tomtebloss/acsi2stm/acsi2stm/TinyFs.cpp

/* ACSI2STM Atari hard drive emulator
 * Copyright (C) 2019-2021 by Jean-Matthieu Coulon
 *
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
 * You should have received a copy of the GNU General Public License
 * along with the program.  If not, see <http://www.gnu.org/licenses/>.
 */

// We are going to torture low-level data structures
// If the library changes too much, it's not guaranteed to work anymore.
#define private public
#include <SdFat.h>
#undef private

#include "Globals.h"

#if ACSI_DRIVER

#include "TinyFs.h"

void TinyPath::getAbsolute(AcsiVolume &volume, AcsiFile *target, oflag_t oflag, AcsiFile *parent) {
  AcsiFile f[2];
  f[0].openRoot(&volume);
  f[1].openRoot(&volume);
  int i = 0;
  for(i = 0; i < maxDepth && f[i & 1] && indexes[i]; ++i) {
    AcsiFile &from = f[i & 1];
    AcsiFile &to = f[~i & 1];
    from.seekSet(((uint32_t)indexes[i] - 1) * 32);
    if(i == maxDepth - 1 || indexes[i + 1] == 0)
      to.openNext(&from, oflag);
    else
      // Directory must be opened in read-only mode
      to.openNext(&from, O_RDONLY);

    if(!to) {
      target->close();
      return;
    }
  }
  *target = f[i & 1];
  if(parent)
    *parent = f[~i & 1];
}

bool TinyPath::getAbsolute(AcsiVolume &volume, char *target, int bufSize) {
  AcsiFile f[2];
  f[0].openRoot(&volume);
  if(!f[0]) {
    // Can't even open root: return empty string
    *target = 0;
    return false;
  }
  *target = '\\';
  ++target;
  --bufSize;
  int i = 0;
  for(i = 0; i < maxDepth && f[i & 1] && indexes[i] && bufSize > 0; ++i) {
    AcsiFile &from = f[i & 1];
    AcsiFile &to = f[~i & 1];
    from.seekSet(((uint32_t)indexes[i] - 1) * 32);
    to.openNext(&from, O_RDONLY);
    if(to) {
      char unicodeName[256];
      to.getName(unicodeName, 256);
      parseUnicodeName(unicodeName);
      int written = nameToAtari(target, bufSize);
      bufSize -= written;
      target += bufSize;
      if(to.isDir() && bufSize) {
        *target = '\\';
        ++target;
        --bufSize;
      }
    }
  }

  // Terminate the string
  if(bufSize > 0)
    *target = 0;
  else
    target[-1] = 0;

  return bufSize > 0;
}

bool TinyPath::set(AcsiVolume &volume, const char *path, int create) {
  // Remove drive letter if any
  if(path[0] && path[1] == ':')
    path += 2;

  int i; // Index in the indexes table;

  if(path[0] == '\\') {
    // Absolute path: start at the beginning
    indexes[0] = 0;
    i = 0;
    ++path;
  } else {
    // Point at the end of the current directory
    for(i = 0; i < maxDepth && indexes[i]; ++i);
  }

  // 2 files to alternate between the two
  AcsiFile f[2];

  // Start with the current path
  getAbsolute(volume, &f[i & 1], O_RDONLY);

  if(!f[i & 1]) {
    indexes[0] = 0;
    return false;
  }

  // Parse path and append to the index list
  while(i < maxDepth - 1 && path[0] && f[i & 1]) {
    AcsiFile &parent = f[i & 1];
    AcsiFile &child = f[~i & 1];

    path = parseAtariPattern(path);
if(create == -1) acsiDbgl("a path=",path," pattern=",pattern," name=",name);

    if(pattern[0] == '.') {
      if(pattern[1] == '.') {
        // "..": Parent directory
        if(i > 0) {
          --i;
          indexes[i] = 0;
          // Need to compute the whole path again to get the parent
          getAbsolute(volume, &child, O_RDONLY);
          if(!child) {
            indexes[0] = 0;
            return false;
          }
        }
      }
      continue;
    }

    // Try to find a matching file

    parent.rewind();
    child.openNext(&parent, O_RDONLY);
    while(child) {
      char childName[256];
      child.getName(childName, 256);
      parseUnicodeName(childName);
      if(matches(pattern))
        break;
      child.openNext(&parent, O_RDONLY);
    }

    if(!child) {
      // No matching file
      if(create) {
        // Check that the name is not a pattern
        for(int i = 0; i < 11; ++i)
          if(pattern[i] == '?')
            // Error: trying to create a file with a wildcard in its name !
            return false;

        // Convert file name to unicode
        char unicodeName[52];
        patternToUnicode(unicodeName, 52);

        if(create == 1) {
          // Create a file
          if(*path)
            // Separator after the file name: a parent directory does not exist.
            return false;

          if(!child.open(&parent, unicodeName, O_RDWR | O_CREAT))
            return false;
        } else if(create == 2) {
          // Create a directory
          if(!child.mkdir(&parent, unicodeName))
            return false;
          if(!child.open(&parent, unicodeName))
            return false;
        } else if(create == -1) {
          // Return true if only the last part is missing
          return !*path;
        }
      }
    }

    if(!child) {
      // Something went wrong, return an error.
      indexes[0] = 0;
      return false;
    }

    indexes[i] = child.dirIndex() + 1;
    ++i;
  }
  indexes[i] = 0;

  return create >= 0;
}

int TinyPath::getNextUnicode(const char *source, char *target) {
  // Forbidden characters
  if(*source && (*source <= ' ' || strchr("*,.:?\\", *source))) {
    *target = '_';
    return 1;
  }

  // Simple 1 byte case
  if(*source < 128) {
    if(*source >= 'a' && *source <= 'z')
      // Convert to upper case
      *target = *source - 'a' + 'A';
    else
      *target = *source;
    return 1;
  }

  // XXX TODO: parse extended unicode and convert it to Atari
  *target = '_';

  // Compute the character length
  int l;
  for(int l = 1; (source[l] & 0b11000000) == 0b1000000; ++l);
  return l;
}

int TinyPath::appendUnicode(char atariChar, char *target, int bufSize) {
  if(bufSize) {
    if(atariChar < 128) {
      *target = atariChar;
      return 1;
    } else {
      // XXX TODO
      *target = '_';
      return 1;
    }
  }
  return 0;
}

int TinyPath::patternToUnicode(char *target, int bufSize) {
  int chars = 0;

  // Expand name
  for(int i = 0; i < 8 && chars < bufSize && pattern[i] != ' '; ++i)
    chars += appendUnicode(pattern[i], &target[chars], bufSize - chars);

  if(pattern[8] != ' ' && chars < bufSize) {
    target[chars] = '.';
    ++chars;
  }

  // Expand extension
  for(int i = 8; i < 11 && chars < bufSize && pattern[i] != ' '; ++i)
    chars += appendUnicode(pattern[i], &target[chars], bufSize - chars);

  // Terminate target string
  if(chars < bufSize) {
    target[chars] = '\0';
    ++chars;
  }

  acsiDbgl("XXX patternToUnicode pattern=",pattern," target=",target);

  return chars;
}

int TinyPath::nameToAtari(char *target, int bufSize) {
  int chars = 0;

  // Expand name
  for(int i = 0; i < 8 && chars < bufSize && name[i] != ' '; ++i) {
    target[chars] = name[i];
    ++chars;
  }

  // Append extension dot if needed
  if(name[8] != ' ' && chars < bufSize) {
    target[chars] = '.';
    ++chars;
  }

  // Expand extension
  for(int i = 8; i < 11 && chars < bufSize && name[i] != ' '; ++i) {
    target[chars] = name[i];
    ++chars;
  }

  return chars;
}

int TinyPath::nameToAtari(AcsiFile *file, char *target, int bufSize) {
  char unicodeName[256];
  file->getName(unicodeName, 256);
  parseUnicodeName(unicodeName);
  return nameToAtari(target, bufSize);
}

bool TinyPath::matches(const char pattern[11]) {
  for(int i = 0; i < 11; ++i) {
    if(pattern[i] != '?' && pattern[i] != name[i])
      return false;
  }
  
  return true;
}

const char * TinyPath::parseAtariPattern(const char *path) {
  int i = 0; // Index in the source string
  int j = 0; // Index in name

  // Parse name
  for(i = 0, j = 0; j < 8 && path[i] && path[i] != '\\' && path[i] != '.'; ++i, ++j) {
    if(path[i] == '*') {
      // Fill with '?' until the end
      for(; j < 8; ++j)
        pattern[j] = '?';
      ++i;
      break;
    }
    pattern[j] = path[i];
  }

  // Fill the name with spaces
  for(; j < 8; ++j)
    pattern[j] = ' ';

  // Point at the first letter of the extension
  while(path[i] && path[i] != '\\' && path[i] != '.')
    ++i;
  if(path[i] == '.')
    ++i;

  // Parse extension
  for(; j < 11 && path[i] && path[i] != '\\'; ++i, ++j) {
    if(path[i] == '*') {
      // Fill with '?' until the end
      for(; j < 11; ++j)
        pattern[j] = '?';
      ++i;
      break;
    }
    pattern[j] = path[i];
  }

  // Fill the extension with spaces
  for(; j < 11; ++j)
    pattern[j] = ' ';

  if(path[i] == '\\')
    ++i;

  return &path[i];
}

const char * TinyPath::parseUnicodeName(const char *path) {
  int i = 0; // Index in the source string
  int j = 0; // Index in name

  int nameEnd;
  int ext;

  // Find the end of the current name
  for(nameEnd = 0; path[nameEnd] && path[nameEnd] != '/'; ++nameEnd);

  // Find the extension
  for(ext = nameEnd - 1; ext > 0 && path[ext] != '.'; --ext);

  if(path[ext] != '.')
    // No extension, put the extension pointer just before the end
    ext = nameEnd;

  // Parse name
  for(i = 0, j = 0; i < ext && j < 8; ++j) {
    if(path[i] == '*') {
      // Fill with '?' until the end
      for(; j < 8; ++j)
        name[j] = '?';
      ++i;
      break;
    }
    i += getNextUnicode(&path[i], &name[j]);
  }

  // Fill the name with spaces
  for(; j < 8; ++j)
    name[j] = ' ';

  // Parse extension
  if(path[ext] == '.') {
    for(i = ext + 1; i < nameEnd && j < 11; ++j) {
      if(path[i] == '*') {
        // Fill with '?' until the end
        for(; j < 11; ++j)
          name[j] = '?';
        ++i;
        break;
      }
      i += getNextUnicode(&path[i], &name[j]);
    }
  }

  // Fill the extension with spaces
  for(; j < 11; ++j)
    name[j] = ' ';

  if(path[nameEnd] == '/')
    ++nameEnd;

  return &path[nameEnd];
}

char TinyPath::name[11];
char TinyPath::pattern[11];

AcsiFile * TinyFile::open(AcsiVolume &volume, TinyPath & path, oflag_t oflag) {
  close();

  path.getAbsolute(volume, &g.f, oflag, &g.dir);

  if(g.f) {
    index = g.f.dirIndex() + 1;
    if(g.dir.isSubDir())
      dirCluster = getCluster(g.dir);
    else
      dirCluster = 0;
    g.dir.seekSet(((uint32_t)index - 1) * 32);
  } else {
    index = 0;
  }

  return &g.f;
}

AcsiFile * TinyFile::acquire(AcsiVolume &volume, oflag_t oflag) {
  if(index
     && g.lastAcquiredCluster == dirCluster
     && g.lastAcquiredIndex == index
     && g.f
     && g.dir
     && ((oflag & O_RDWR) ? g.f.isWritable() : true)
  ) {
    // Optimized !
    return &g.f;
  }

  g.f.close();

  if(!index) {
    // File closed
    g.lastAcquiredIndex = 0;
    return &g.f;
  }

  // Open the parent directory in g.dir
  if(!dirCluster) {
    // File is in the root directory
    g.dir.openRoot(&volume);
  } else {
    // Find any directory to inject data into the structure (evil grin)
    g.f.openRoot(&volume);
    while(g.dir.openNext(&g.f, O_RDONLY) && !g.dir.isDirectory());
    if(g.dir) {
      // Found a directory handle to inject the cluster in it
      setCluster(g.dir, dirCluster);
    } else {
      // Should never happen
      close();
    }
  }

  // Find the file with the correct index
  g.f.open(&g.dir, index - 1, oflag);

  if(g.f) {
    g.lastAcquiredCluster = dirCluster;
    g.lastAcquiredIndex = index;
  } else {
    g.lastAcquiredIndex = 0;
  }

  return &g.f;
}

void TinyFile::close() {
  g.f.close();
  index = 0;
  g.lastAcquiredIndex = 0;
}

AcsiFile * TinyFile::openNext(AcsiVolume &volume, oflag_t oflag, const char pattern[11]) {
  acquire(volume, O_RDONLY);

  if(!g.f) {
    close();
    return &g.f;
  }

  if(g.dir)
    findNextMatching(pattern, oflag);

  // Update the index
  if(g.f)
    index = g.f.dirIndex() + 1;
  else
    index = 0;

  return &g.f;
}

AcsiFile * TinyFile::openFirst(AcsiVolume &volume, oflag_t oflag, const char pattern[11]) {
  close();

  if(g.dir) {
    g.dir.rewind();
    findNextMatching(pattern, oflag);
  }

  // Update the index
  if(g.f) {
    index = g.f.dirIndex() + 1;
    g.dir.seekSet(((uint32_t)index - 1) * 32);
  } else {
    index = 0;
  }

  return &g.f;
}

AcsiFile * TinyFile::openFirst(AcsiVolume &volume, TinyPath &path, oflag_t oflag, const char pattern[11]) {
  close();

  path.getAbsolute(volume, &g.dir);
  if(g.dir)
    findNextMatching(pattern, oflag);

  if(g.f) {
    index = g.f.dirIndex() + 1;
    if(g.dir.isSubDir())
      dirCluster = getCluster(g.dir);
    else
      dirCluster = 0;
  } else {
    index = 0;
  }

  return &g.f;
}

void TinyFile::findNextMatching(const char pattern[11], oflag_t oflag) {
  g.f.openNext(&g.dir, oflag);
  while(g.f) {
    char name[256];
    g.f.getName(name, 256);
    TinyPath::parseUnicodeName(name);
    if(TinyPath::matches(pattern))
      break;
    g.f.openNext(&g.dir, oflag);
  }
}

uint32_t TinyFile::getCluster(AcsiFile &f) {
  uint32_t cluster;
  uint64_t position = f.curPosition();
  f.rewind();
  if(f.m_fFile)
    cluster = f.m_fFile->m_firstCluster;
  else
    cluster = f.m_xFile->m_firstCluster;
  f.seekSet(position);
  return cluster;
}

void TinyFile::setCluster(AcsiFile &f, uint32_t cluster) {
  f.rewind();
  if(f.m_fFile)
    f.m_fFile->m_firstCluster = cluster;
  else
    f.m_xFile->m_firstCluster = cluster;
}

// Global variables for TinyFile
TinyFile::Global TinyFile::g;

int TinyFileDescriptor::read(AcsiVolume &volume, uint8_t *data, int bytes) {
  AcsiFile *f = acquire(volume);
  if(!f->seekSet(position))
    return -1;

  int r = f->read(data, bytes);
  if(r > 0)
    position += r;

  return r;
}

int TinyFileDescriptor::write(AcsiVolume &volume, uint8_t *data, int bytes) {
  AcsiFile *f = acquire(volume, O_RDWR);
  if(!f->seekSet(position))
    return -1;

  int r = f->write(data, bytes);
  if(r > 0)
    position += r;

  return r;
}

#endif
