tomtebloss/acsi2stm/acsi2stm/DmaPort.h

/* ACSI2STM Atari hard drive emulator
 * Copyright (C) 2019-2021 by Jean-Matthieu Coulon
 *
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
 * You should have received a copy of the GNU General Public License
 * along with the program.  If not, see <http://www.gnu.org/licenses/>.
 */

#ifndef DMA_PORT_H
#define DMA_PORT_H

#include "Globals.h"
#include "Watchdog.h"

struct DmaPort {
  static void init();
  void begin(uint8_t deviceMask = 0);

  // Add a device ID to the mask
  void addDevice(int id) {
    deviceMask |= 1<<id;
  }

  // Remove a device ID from the mask
  void removeDevice(int id) {
    deviceMask &=~ (1<<id);
  }

  // Return true if the ACSI bus is idle:
  // IRQ, DRQ and ACK are high.
  static bool idle();

  // Wait until the bus is ready.
  // Uses input pull-down to detect that the ST is actually powered on.
  void waitBusReady();

  // Wait for a command on the bus.
  //
  // This function never never fails but may trigger the watchdog.
  // Returns the command byte. You can use cmdDeviceId and cmdCommand to parse it.
  uint8_t waitCommand();

  // Returns the device ID for a given command byte.
  static uint8_t cmdDeviceId(uint8_t cmd) {
    return cmd >> 5;
  }

  // Read bytes using the IRQ/CS method.
  static void readIrq(uint8_t *bytes, int count);

  // Read one byte using the IRQ/CS method.
  static uint8_t readIrq();

  // Send one byte using the IRQ/CS method.
  // This is normally used for the status byte.
  static void sendIrq(uint8_t byte);

  // Read bytes using the DRQ/ACK method.
  // count must be a multiple of 16.
  static void read(uint8_t *bytes, int count);

  // Read to dataBuf.
  void read(int count = ACSI_BLOCKSIZE) {
    read(dataBuf, count);
  }

  // Send bytes using the DRQ/ACK method.
  // count must be a multiple of 16.
  static void send(const uint8_t *bytes, int count);
  
  // Send data in dataBuf.
  void send(int count = ACSI_BLOCKSIZE) {
    send(dataBuf, count);
  }

  Watchdog watchdog;

  uint8_t dataBuf[ACSI_BLOCKSIZE];
protected:
  // Low level pin manipulation methods
  static void releaseDrq();
  static void releaseIrq();
  static void releaseDataBus();
  static void acquireDrq();
  static void acquireDataBus();
  static uint8_t waitCs();
  static uint8_t waitA1();
  static bool readAck();
  static void pullIrq();
  static bool pullDrqUntilAck();
  static void writeData(uint8_t byte);

  // Device initialization
  static void setupDrqTimer();
  static void setupCsTimer();
  static void setupGpio();

public: // XXX
  uint8_t deviceMask;
};

// vim: ts=2 sw=2 sts=2 et
#endif
