tomtebloss/acsi2stm/acsi2stm/boot.h

unsigned char boot_bin[] = {
  0x48, 0xe7, 0xff, 0xfe, 0x41, 0xfa, 0x01, 0x62, 0x8f, 0x10, 0xea, 0x0f,
  0x41, 0xfa, 0x01, 0x6b, 0xdf, 0x10, 0x48, 0x79, 0x00, 0x00, 0x0c, 0x00,
  0x3f, 0x3c, 0x00, 0x48, 0x4e, 0x41, 0x5c, 0x4f, 0x4a, 0x80, 0x67, 0x42,
  0x2c, 0x40, 0x61, 0x00, 0x00, 0xba, 0x4a, 0x00, 0x66, 0x26, 0x2f, 0x3c,
  0x00, 0x00, 0x0b, 0xde, 0x2f, 0x0e, 0x3f, 0x3c, 0x00, 0x4a, 0x4e, 0x41,
  0x4f, 0xef, 0x00, 0x0a, 0x4e, 0x96, 0x4a, 0x00, 0x67, 0x28, 0x2f, 0x0e,
  0x3f, 0x3c, 0x00, 0x49, 0x4e, 0x41, 0x5c, 0x4f, 0x60, 0x00, 0x00, 0x1c,
  0x2f, 0x0e, 0x3f, 0x3c, 0x00, 0x49, 0x4e, 0x41, 0x5c, 0x4f, 0x48, 0x7a,
  0x01, 0x43, 0x60, 0x00, 0x00, 0x64, 0x48, 0x7a, 0x01, 0x2b, 0x60, 0x00,
  0x00, 0x5c, 0x41, 0xfa, 0xff, 0x90, 0x4a, 0x28, 0x01, 0xb5, 0x67, 0x64,
  0x11, 0x7c, 0x00, 0x20, 0x01, 0x69, 0x11, 0x7c, 0x00, 0x01, 0x01, 0x6c,
  0x43, 0xe8, 0x02, 0x00, 0x30, 0x3c, 0x00, 0x7f, 0x22, 0xd8, 0x51, 0xc8,
  0xff, 0xfc, 0x43, 0xfa, 0xff, 0x6c, 0x20, 0x09, 0x60, 0x00, 0x02, 0x02,
  0x61, 0x44, 0x4a, 0x00, 0x67, 0x06, 0x48, 0x7a, 0x00, 0xe2, 0x60, 0x20,
  0x48, 0x7a, 0x00, 0xc3, 0x3f, 0x3c, 0x00, 0x09, 0x4e, 0x41, 0x5c, 0x4f,
  0x48, 0x7a, 0x00, 0xc6, 0x3f, 0x3c, 0x00, 0x09, 0x4e, 0x41, 0x5c, 0x4f,
  0x4c, 0xdf, 0x7f, 0xff, 0x60, 0x00, 0xfd, 0x3a, 0x48, 0x7a, 0x00, 0xa3,
  0x3f, 0x3c, 0x00, 0x09, 0x4e, 0x41, 0x5c, 0x4f, 0x3f, 0x3c, 0x00, 0x09,
  0x4e, 0x41, 0x5c, 0x4f, 0x4c, 0xdf, 0x7f, 0xff, 0x4e, 0x75, 0x50, 0xf8,
  0x04, 0x3e, 0x41, 0xfa, 0x00, 0x80, 0x43, 0xf8, 0x86, 0x06, 0x45, 0xf8,
  0x86, 0x04, 0x32, 0xbc, 0x01, 0x90, 0x32, 0xbc, 0x00, 0x90, 0x11, 0xc0,
  0x86, 0x0d, 0xe0, 0x88, 0x11, 0xc0, 0x86, 0x0b, 0xe0, 0x48, 0x11, 0xc0,
  0x86, 0x09, 0x70, 0x00, 0x10, 0x28, 0x00, 0x04, 0x34, 0x80, 0x32, 0xbc,
  0x00, 0x88, 0x22, 0x3c, 0x00, 0x00, 0x00, 0x8a, 0x74, 0x04, 0x48, 0x41,
  0x12, 0x18, 0x48, 0x41, 0x24, 0x81, 0x61, 0x20, 0x51, 0xca, 0xff, 0xf4,
  0x24, 0xbc, 0x00, 0x00, 0x00, 0x00, 0x61, 0x14, 0x32, 0xbc, 0x00, 0x8a,
  0x30, 0x12, 0x32, 0xbc, 0x01, 0x80, 0x32, 0xbc, 0x00, 0x80, 0x51, 0xf8,
  0x04, 0x3e, 0x4e, 0x75, 0x20, 0x3c, 0x00, 0x00, 0x02, 0x58, 0xd0, 0xb8,
  0x04, 0xba, 0xb0, 0xb8, 0x04, 0xba, 0x6d, 0x0a, 0x08, 0x38, 0x00, 0x05,
  0xfa, 0x01, 0x66, 0xf2, 0x4e, 0x75, 0x70, 0xff, 0x58, 0x8f, 0x60, 0xd2,
  0x08, 0xe0, 0x00, 0x00, 0x06, 0x41, 0x43, 0x53, 0x49, 0x20, 0x64, 0x65,
  0x76, 0x69, 0x63, 0x65, 0x20, 0x30, 0x20, 0x00, 0x62, 0x6f, 0x6f, 0x74,
  0x69, 0x6e, 0x67, 0x0d, 0x0a, 0x00, 0x62, 0x6f, 0x6f, 0x74, 0x20, 0x65,
  0x72, 0x72, 0x6f, 0x72, 0x0d, 0x0a, 0x00, 0x4d, 0x61, 0x6c, 0x6c, 0x6f,
  0x63, 0x20, 0x66, 0x61, 0x69, 0x6c, 0x65, 0x64, 0x0d, 0x0a, 0x00, 0x44,
  0x4d, 0x41, 0x20, 0x65, 0x72, 0x72, 0x6f, 0x72, 0x0d, 0x0a, 0x00, 0x00,
  0x00, 0x00, 0x00, 0x00, 0x00, 0x00, 0x00, 0x00, 0x45, 0xfa, 0x09, 0x1c,
  0x41, 0xd2, 0x30, 0x3c, 0x02, 0xbf, 0x42, 0x18, 0x51, 0xc8, 0xff, 0xfc,
  0x25, 0x7c, 0x09, 0x1f, 0x28, 0xe0, 0x00, 0x00, 0x8f, 0x2a, 0x00, 0x01,
  0x25, 0x78, 0x04, 0xc2, 0x00, 0x7c, 0x30, 0x38, 0x04, 0xa6, 0x53, 0x40,
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
};
unsigned int boot_bin_len = 3478;
